TobiasVanDyk/Building-the-Advanced-Preamplifier-1976-Douglas-Self/AudioSwitchBox-3Way/3.5mm Jack socket 3 pole.jpg

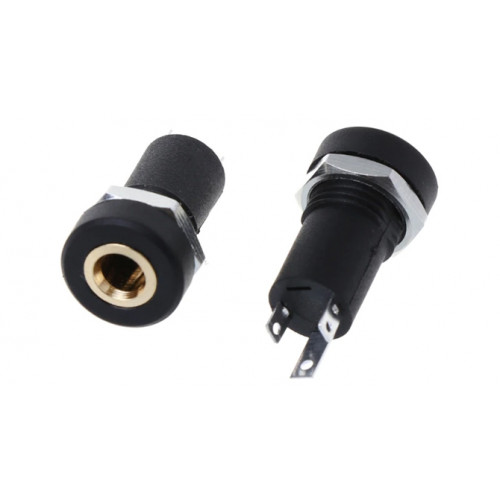
AudioSwitchBox-3Way/3.5mm Jack socket 3 pole.jpg
