TobiasVanDyk/Building-the-Advanced-Preamplifier-1976-Douglas-Self/AudioSwitchBox-3Way/TS-23E01AT15.jpg

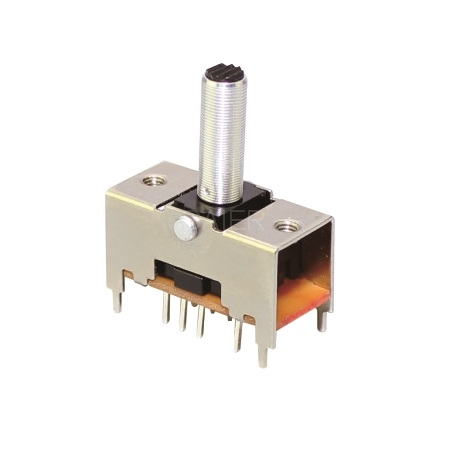
AudioSwitchBox-3Way/TS-23E01AT15.jpg
